GitX123/MoDisp/back-end/MoDisp/front-end/image/bg_empty_128.png

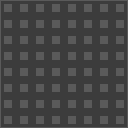
back-end/MoDisp/front-end/image/bg_empty_128.png
